qmat/chandelier_documentation/files/pictures_Hannstar_HSD170ME13/photo1.JPG

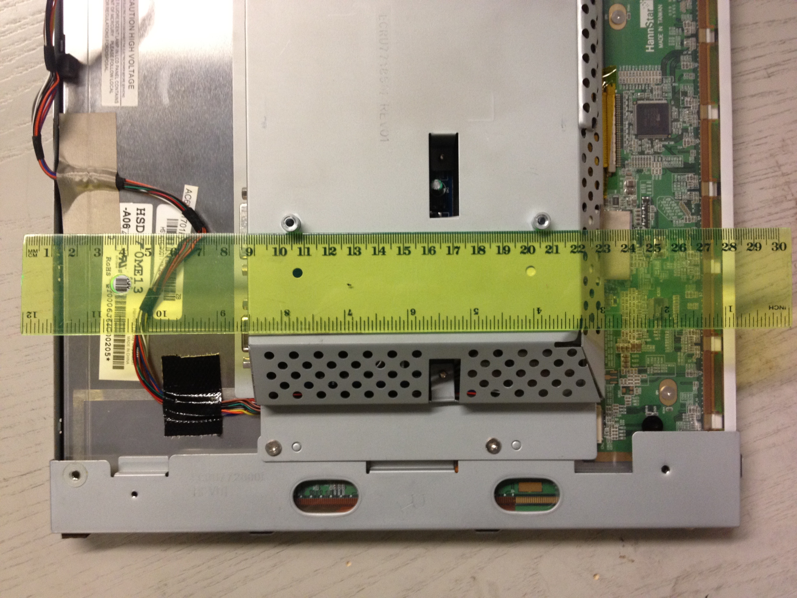
files/pictures_Hannstar_HSD170ME13/photo1.JPG
