qmat/chandelier_documentation/files/pictures_Hannstar_HSD170ME13/photo2.JPG

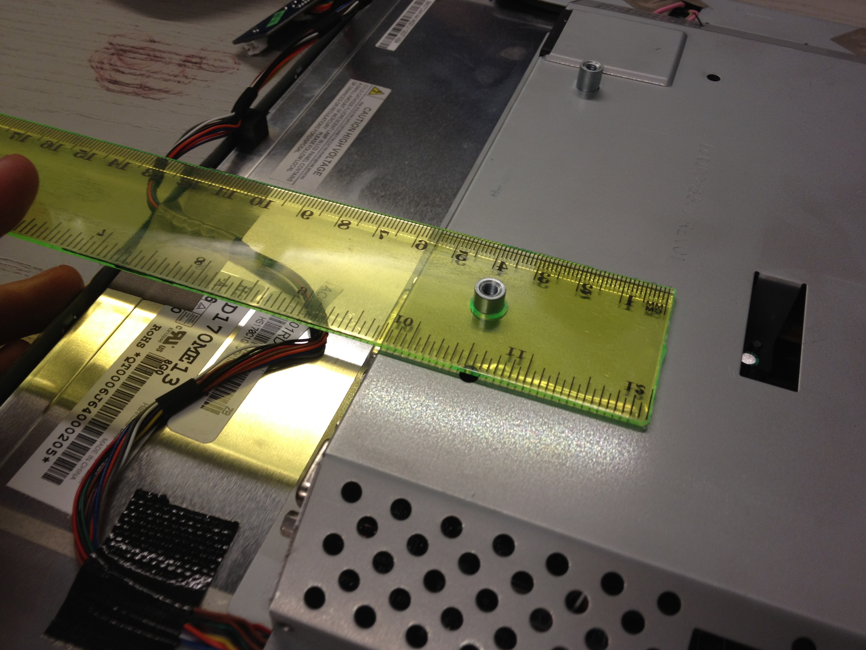
files/pictures_Hannstar_HSD170ME13/photo2.JPG
