qmat/chandelier_documentation/files/pictures_Hannstar_HSD170ME13/photo4.JPG

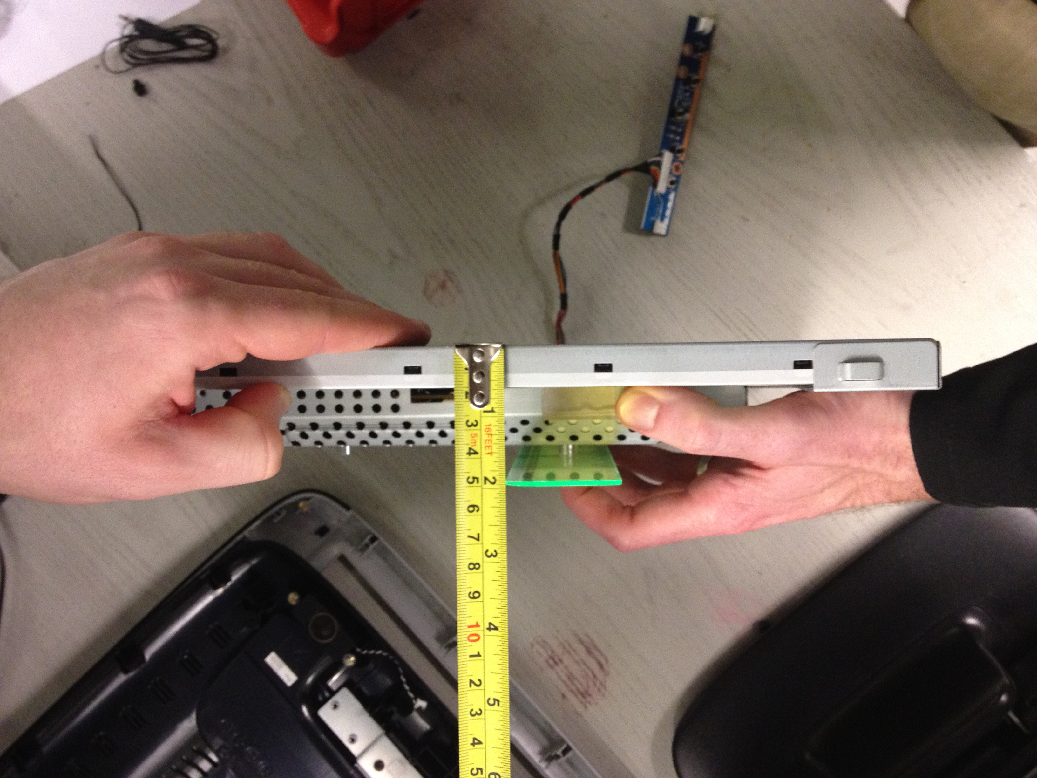
files/pictures_Hannstar_HSD170ME13/photo4.JPG
