qmat/chandelier_documentation/files/pictures_Hannstar_HSD170ME13/photo5.JPG

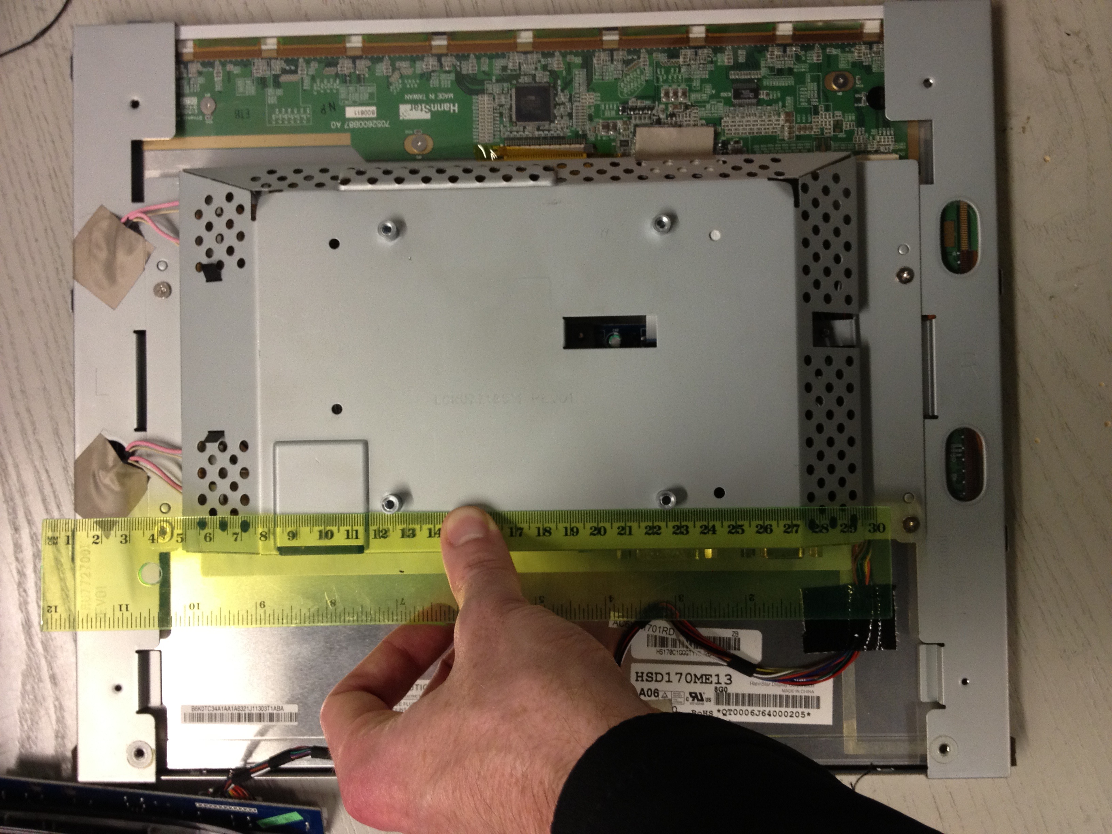
files/pictures_Hannstar_HSD170ME13/photo5.JPG
