qmat/chandelier_documentation/files/pictures_Hannstar_HSD170ME13/photo6.JPG

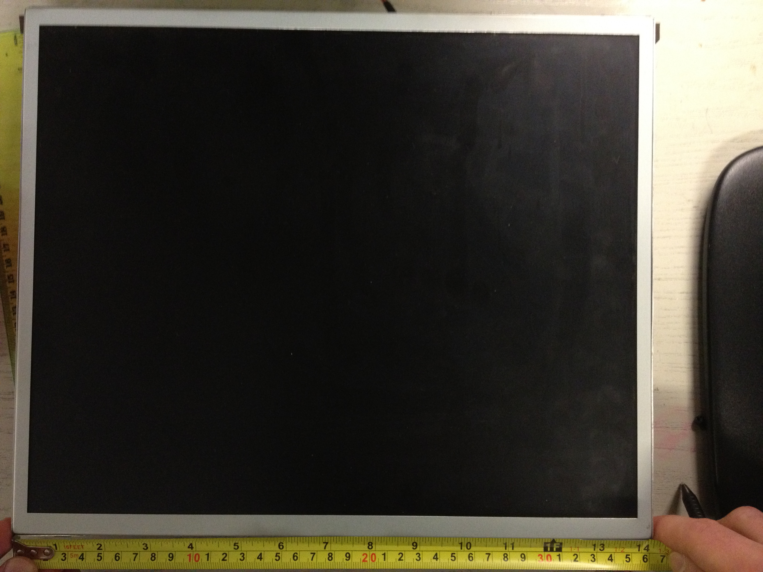
files/pictures_Hannstar_HSD170ME13/photo6.JPG
