qmat/chandelier_documentation/files/rhino_models/chandelier/chandelier_screenshot1.png

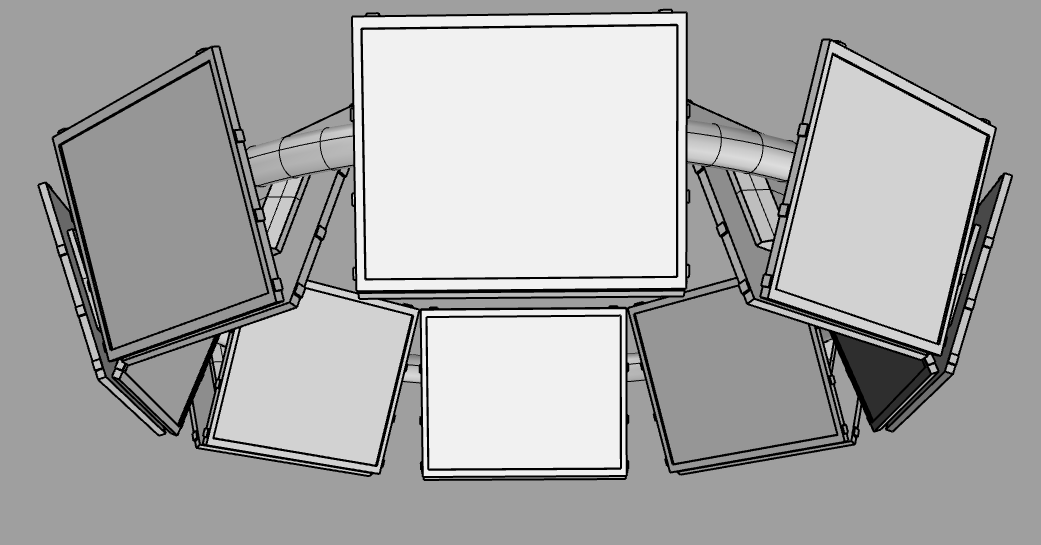
files/rhino_models/chandelier/chandelier_screenshot1.png
