qmat/chandelier_documentation/files/rhino_models/chandelier/chandelier_screenshot3.png

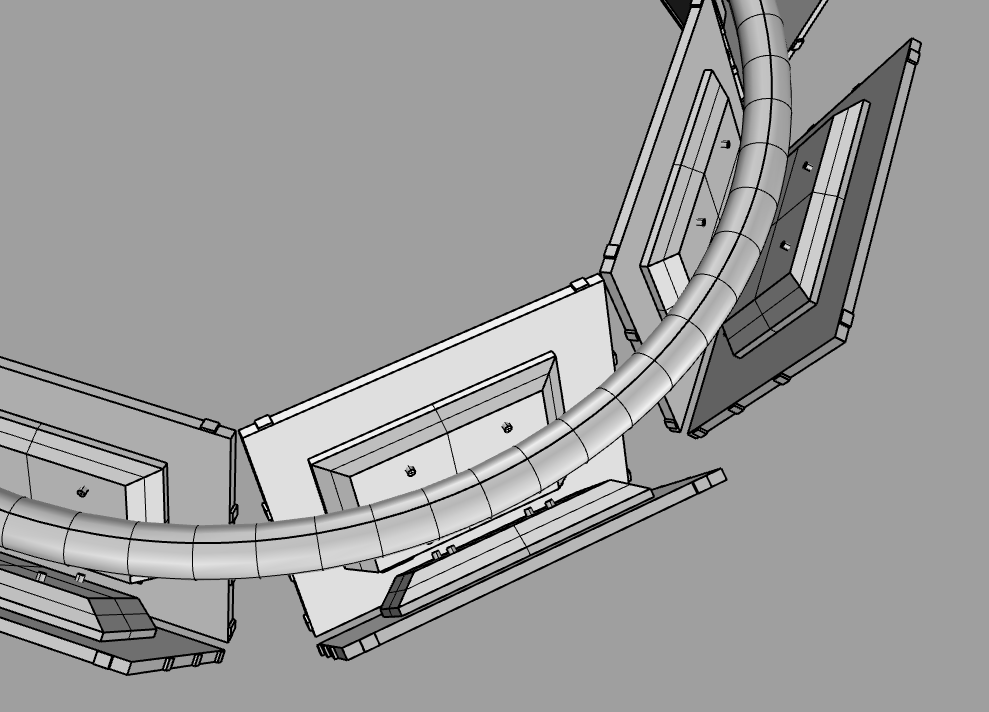
files/rhino_models/chandelier/chandelier_screenshot3.png
