qmat/chandelier_documentation/files/safety_documentation/envelope.tif

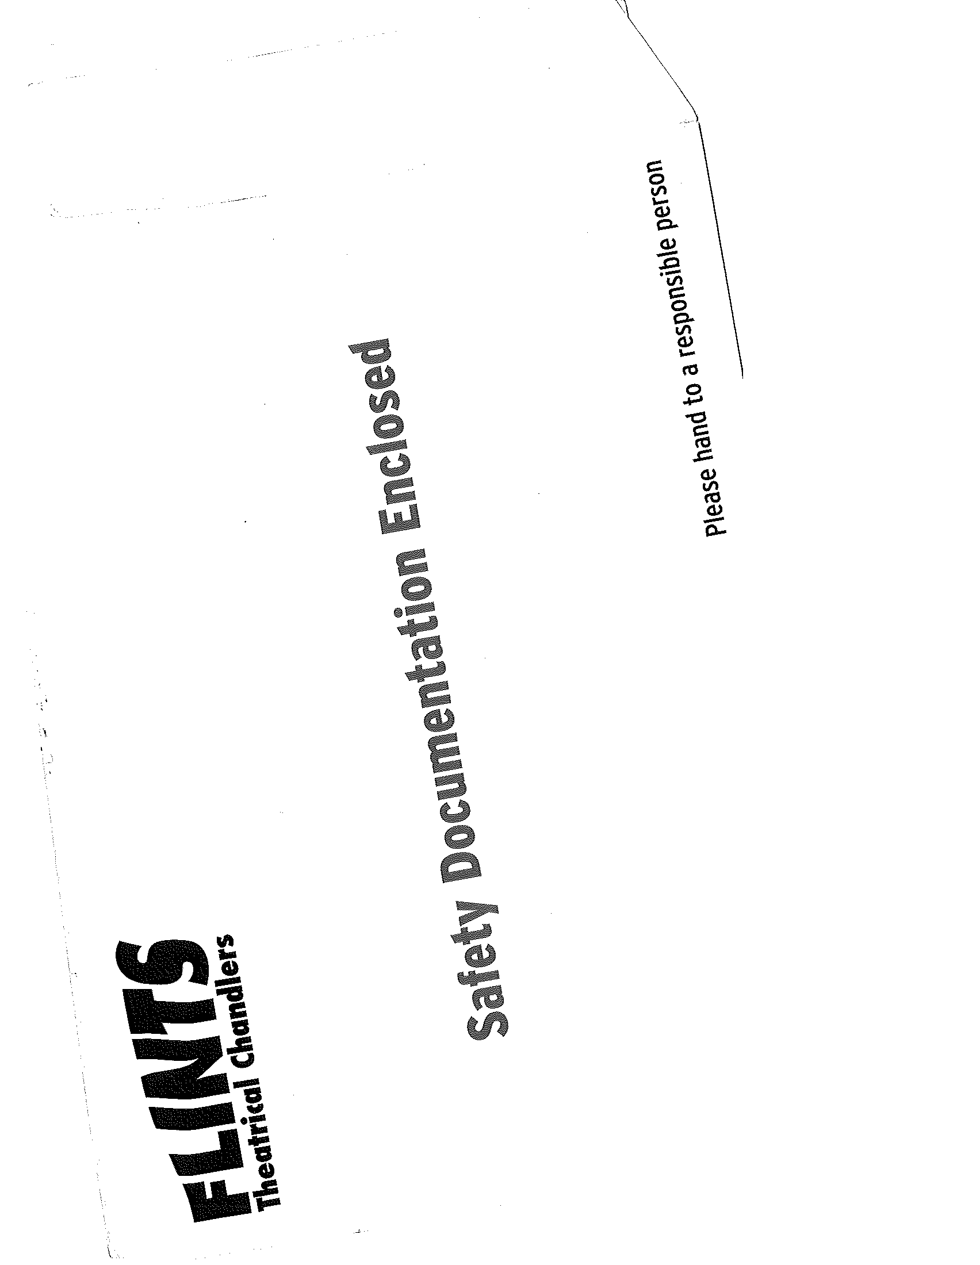
files/safety_documentation/envelope.tif
