qmat/chandelier_documentation/files/safety_documentation/reutlinger_documentation2.tif

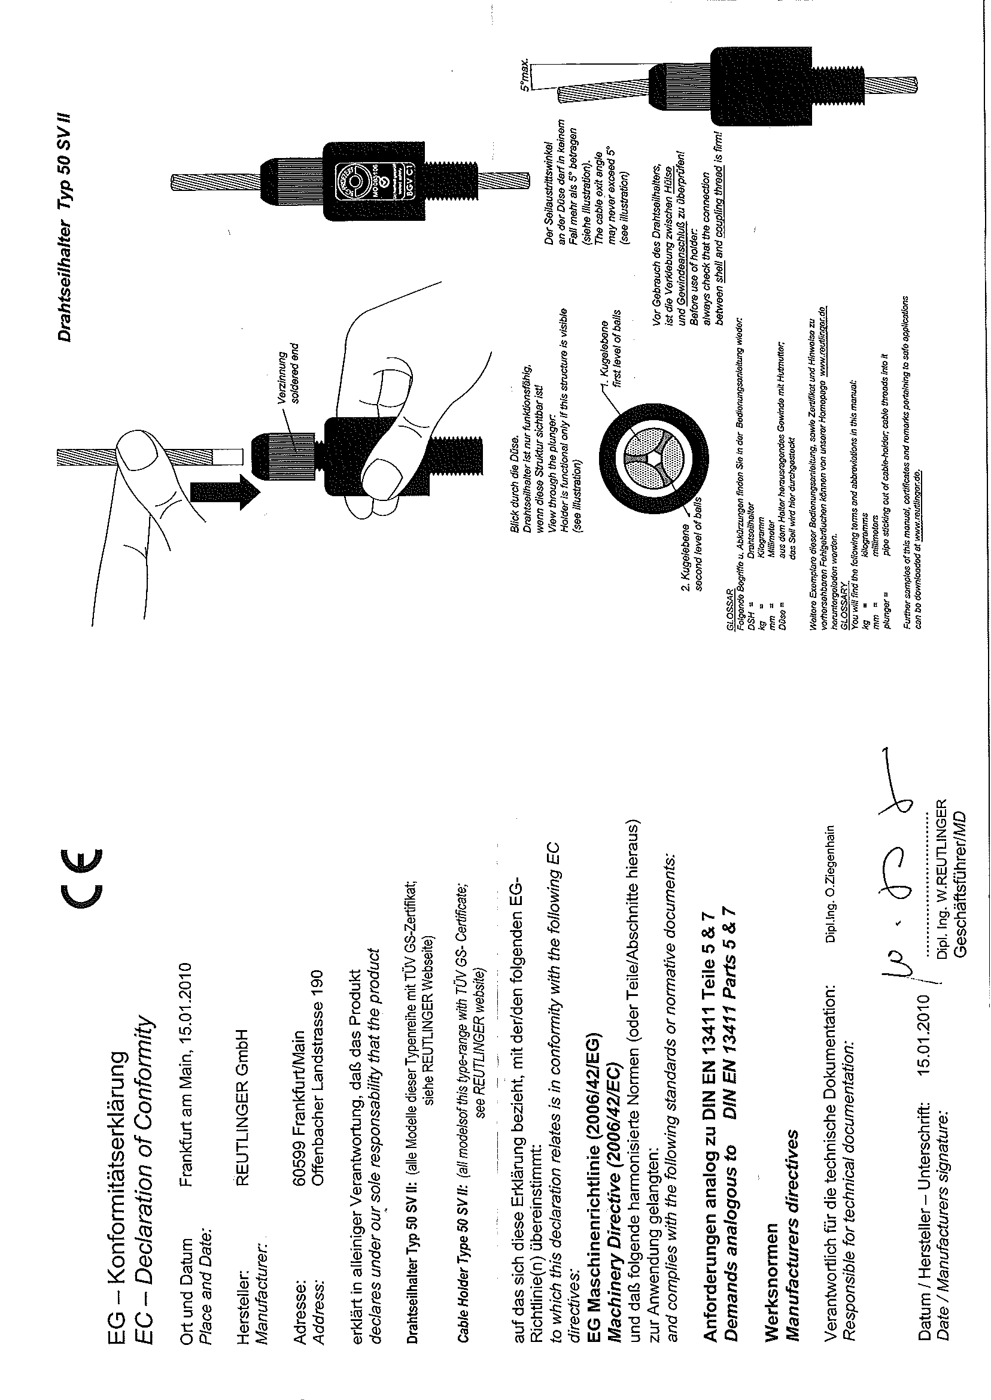
files/safety_documentation/reutlinger_documentation2.tif
