qmat/chandelier_documentation/files/software/deployment.graffle/image1.tiff

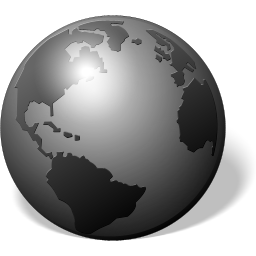
files/software/deployment.graffle/image1.tiff
