qmat/chandelier_documentation/files/safety_documentation/tube_order.tif

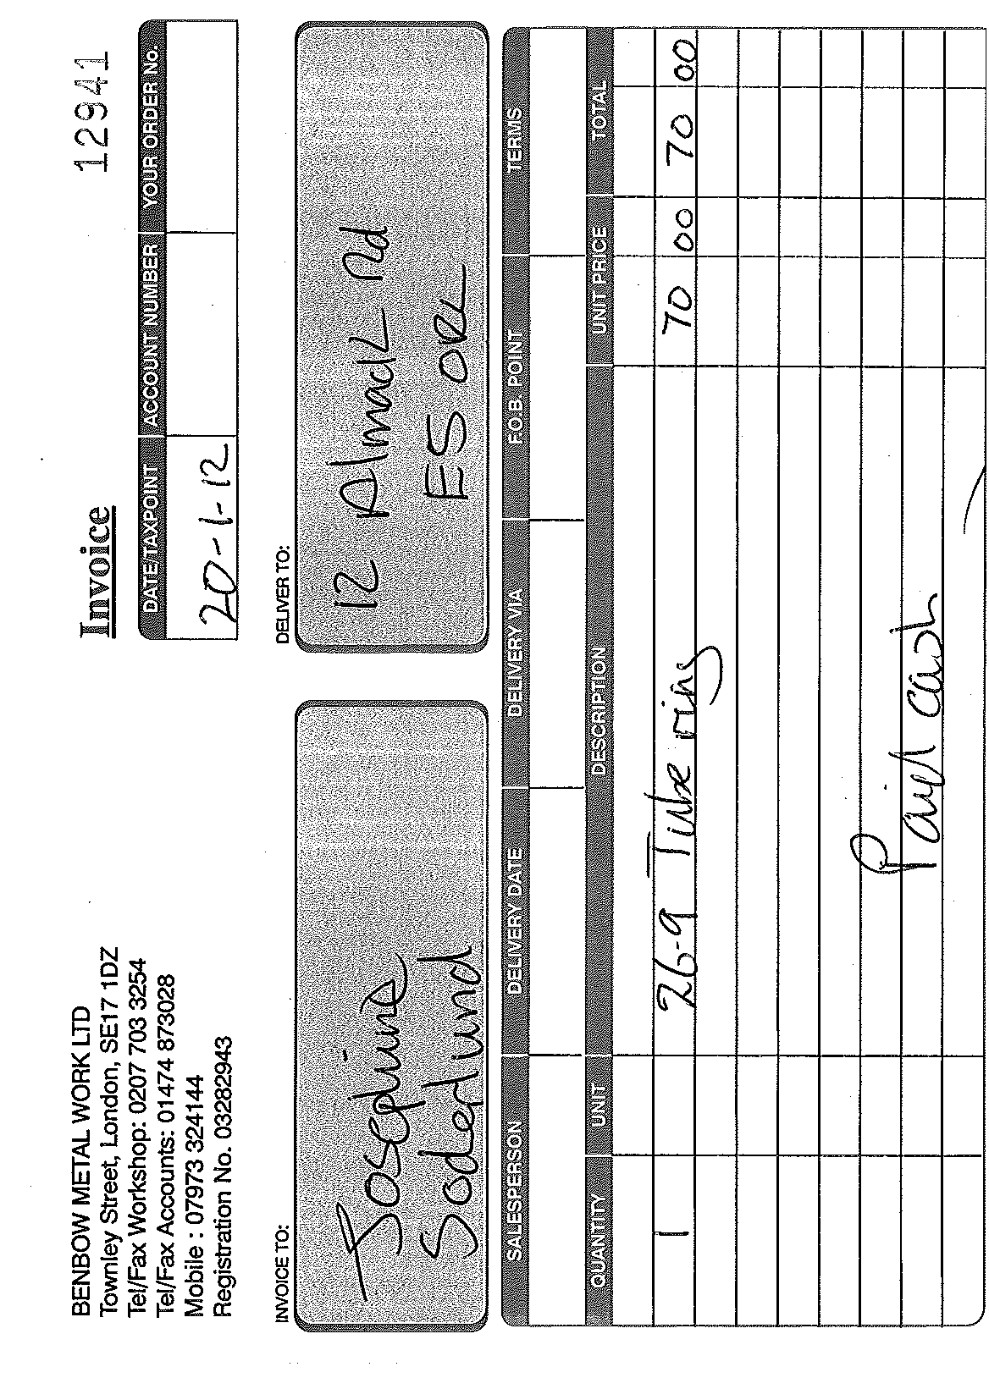
files/safety_documentation/tube_order.tif
